juepi/RC-MultiSwitcher/Code/include/common-functions.h

/*
*   Common Function declarations
*/
#ifndef COMMON_FUNCTIONS_H
#define COMMON_FUNCTIONS_H

#include <Arduino.h>

extern void ToggleLed(int PIN, int WaitTime, int Count);

#endif //COMMON_FUNCTIONS_H
