juepi/RC-MultiSwitcher/Code/src/common-functions.cpp

/*
 * Common Functions
 */
#include <Arduino.h>
#include "common-functions.h"

void ToggleLed(int PIN, int WaitTime, int Count)
{
    // Toggle digital output
    for (int i = 0; i < Count; i++)
    {
        digitalWrite(PIN, !digitalRead(PIN));
        delay(WaitTime);
    }
}
